CarloMara/didactic-octo-PSU/basette/basetta_lineare/lineare_rev3/docs/SR_Passives-1801.pdf

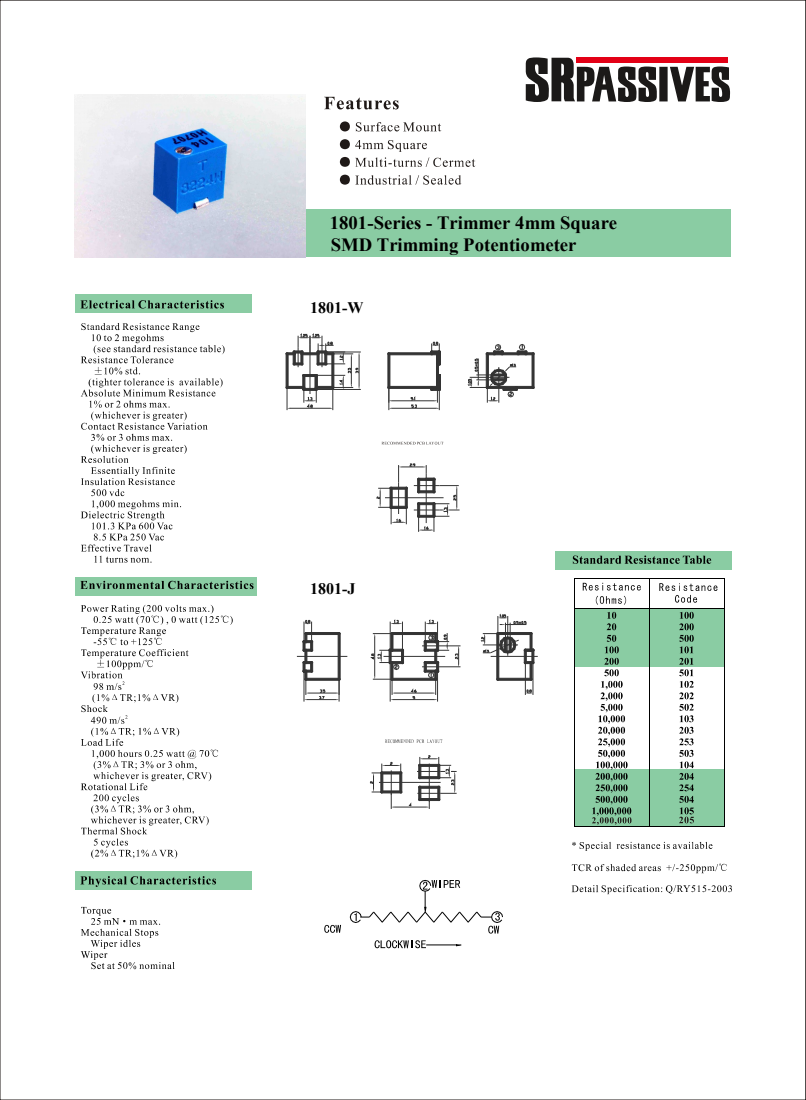
[picture p15: page 1]

1801-Series - Trimmer 4mm Square
SMD Trimming Potentiometer
