CarloMara/didactic-octo-PSU/basette/basetta_lineare/lineare_cv/output.pdf/alimentatore.pdf

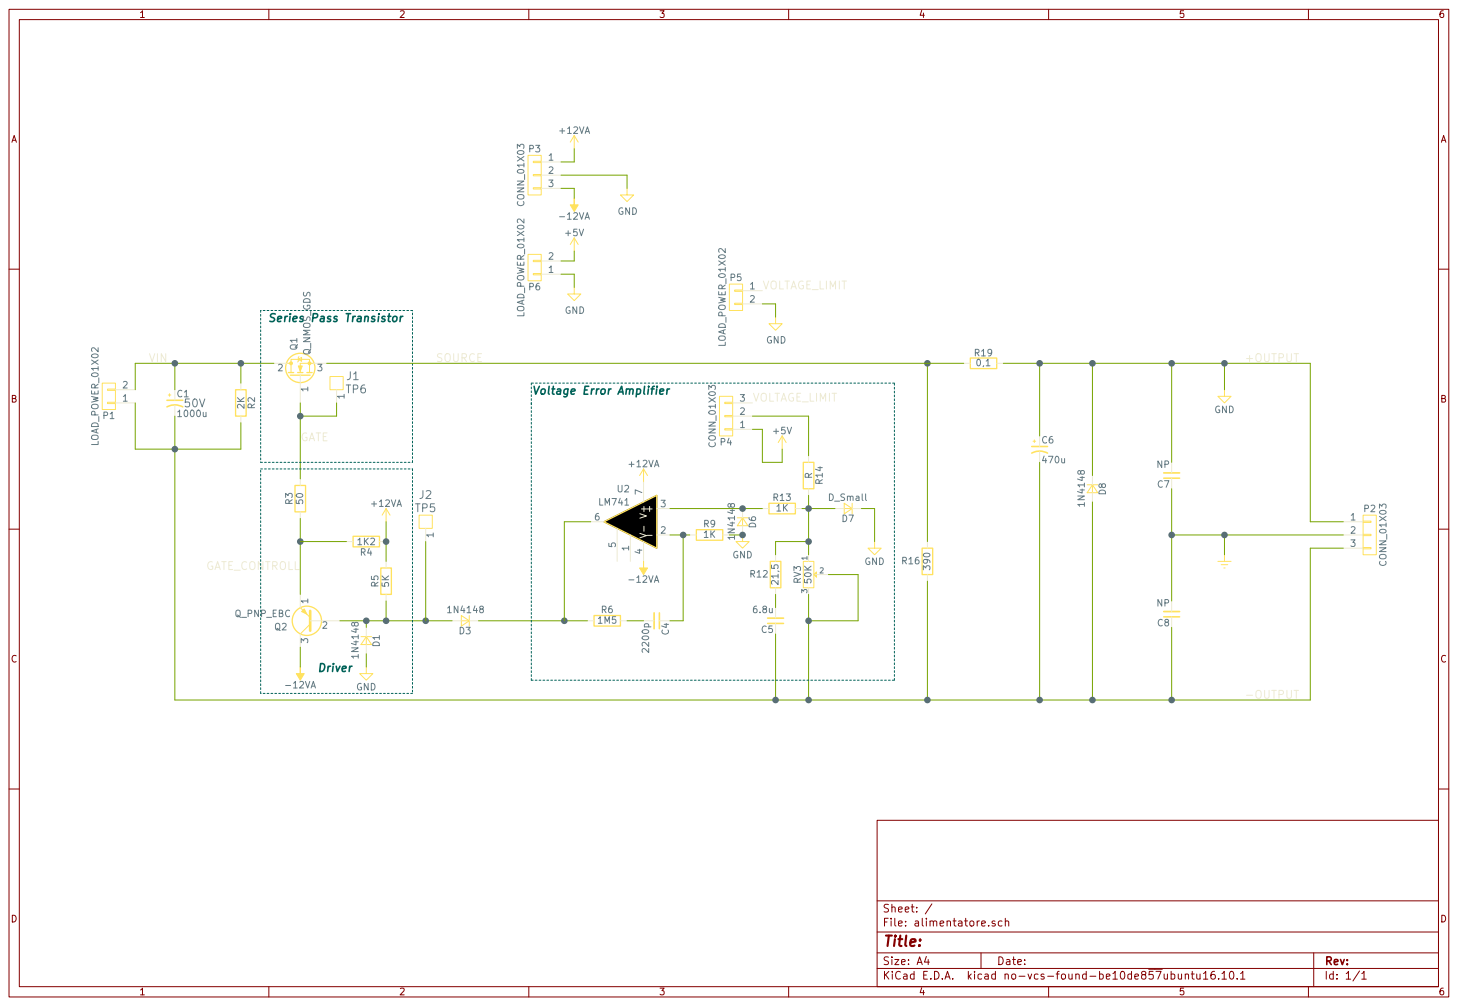
[picture p18: page 1]

Id: 1/1 Title: File: alimentatore.sch Sheet: /
