CarloMara/didactic-octo-PSU/basette/basetta_lineare/lineare_cv/output/alimentatore.pdf

Id: 1/1 Title: File: alimentatore.sch Sheet: /
