CarloMara/didactic-octo-PSU/simulazioni_spice/boost_buck.asc

C1: cap; 10µ; Rser=.01
C3: cap; 68n
C4: cap; 68n
C5: cap; 4.7µ
C6: cap; 4700p
C7: cap; 10p
C8: cap; 22µ; x2; Rser=.005
C9: cap; 470p
C11: cap; 10n
D1: schottky; PMEG2010AEB
L1: ind; 6.8µ; Ipk=5.94 Rser=0.014018 Rpar=640.56 Cpar=0 mfg="Coilcraft" pn="MSS1048-682"
Q1: pnp; 2N3906
R4: res; 27.4K
R5: res; 21K
R6: res; 10K
R7: res; 3k
U1: LTC3114-1
V1: voltage; 12
V2: voltage; 21
Named nets: 0, IN, OUT
.tran 3m startup
LTC3114-1 - 40V, 1A Synchronous Buck-Boost DC/DC Converter with Programmable Output Current 
Wide Vin Range Regulator with Bootstrapped LDO
Input: 2.7V to 40V     Output: 5V @ 1A for Vin > Vout
Notes: 
  If the simulation model is not found please update with the "Sync Release" command from the "Tools" menu.
  It remains the customer's responsibility to verify proper and reliable operation in the actual application.
  Component substitution and printed circuit board layout may significantly affect circuit performance or reliability.
  Contact your local sales representative for assistance. This circuit is distributed to customers only for use with LTC parts.
  Copyright © 2015 Linear Technology Inc.  All rights reserved.
D1 Improves 
Efficiency at High Vin
