CarloMara/didactic-octo-PSU/simulazioni_spice/switching_tracking/Switching_Follower_pass.asc

C1: POLCAP; 230µ; Rser=0.05
C2: POLCAP; 250µ; Rser=0.07
C3: cap; .01µ
C4: cap; 470p
C6: cap; 2200pf
D1: schottky; MBRS140
D2: diode; 1N4148
L1: IND; 50µ
M1: nmos; IRF510
Q1: pnp; 2N3906
Q2: pnp; 2N3906
R1: RES; 2.7K
R2: res; 10K
R3: res; 3k
R4: res; 1.5m
R5: res; 8k
R6: res; 5
R7: res; 10k
R8: res; 150k
R9: res; 5k
R10: res; 1.2k
U1: LT1074
U2: OP27
V1: VOLTAGE; 30; Rser=0.02
V2: voltage; 12
V3: voltage; 12
V4: voltage; 5
Named nets: 0, PREREG_OUT, IN, OUT, v+, v-, 5v, vgnd
.tran 10m uic
