CarloMara/didactic-octo-PSU/simulazioni_spice/switching_tracking/LT1074_TA01.asc

C1: POLCAP; 230µ; Rser=0.05
C2: POLCAP; 500µ; Rser=0.07
C3: cap; .01µ
D1: schottky; MBRS140
L1: IND; 50µ
R1: RES; 2.7K
R2: RES; 2.21K
R3: RES; 2.8K
Rload: res; 1
U1: LT1074
V1: VOLTAGE; 25; Rser=0.02
Named nets: 0, OUT, IN
.tran 2m startup
LT1074 - Step-Down Switching Regulator
Input: 10V to 40V       Output: 5V @ 5A
Note:
  If the simulation model is not found please update with the "Sync Release" command from the "Tools" menu.
  It remains the customer's responsibility to verify proper and reliable operation in the actual application.
  Component substitution and printed circuit board layout may significantly affect circuit performance or reliability.
  Contact your local sales representative for assistance. This circuit is distributed to customers only for use with LTC parts.
  Copyright © 2011 Linear Technology Inc. All rights reserved.
