CarloMara/didactic-octo-PSU/simulazioni_spice/switching_tracking/Switching_Follower.asc

C1: POLCAP; 230µ; Rser=0.05
C2: POLCAP; 500µ; Rser=0.07
C3: cap; .01µ
C4: cap; 470p
C5: cap; 100µ
D1: schottky; MBRS140
I1: current; SINE(1 1 1k)
L1: IND; 50µ
Q1: pnp; 2N3906
R1: RES; 2.7K
R2: res; 10K
R3: res; 5K
U1: LT1074
U2: LT3083
V1: VOLTAGE; 25; Rser=0.02
V2: VOLTAGE; 10; Rser=0.02
Named nets: 0, PREREG_OUT, IN, OUT
.tran 0 10m 4m
LT1074 - Step-Down Switching Regulator
Input: 10V to 40V       Output: 5V @ 5A
Note:
  If the simulation model is not found please update with the "Sync Release" command from the "Tools" menu.
  It remains the customer's responsibility to verify proper and reliable operation in the actual application.
  Component substitution and printed circuit board layout may significantly affect circuit performance or reliability.
  Contact your local sales representative for assistance. This circuit is distributed to customers only for use with LTC parts.
  Copyright © 2011 Linear Technology Inc. All rights reserved.
