CarloMara/didactic-octo-PSU/simulazioni_spice/varie/Draft1.asc

C1: cap; 2200pf
D1: diode; 1N4148
M1: nmos; BSZ42DN25NS3
Q1: pnp; 2N3906
R1: res; 1.5m
R2: res; 8k
R3: res; 10k
R4: res; 50k
R5: res; 5k
R6: res; 1.2k
R7: res; 100k
U1: OP27
V1: voltage; 12
V2: voltage; 12
V3: voltage; 5
V4: voltage; 40
Named nets: v-, v+, 0, 5v, vgnd
.tran 5m
