CarloMara/didactic-octo-PSU/simulazioni_spice/varie/LT3081_LT8612_LTC3632_LT3092_DC2132A.asc

C1: cap; .01µ
C2: cap; 1µ
C3: cap; .1µ
C4: cap; 10µ; x5; Rser=0.005
C6: cap; 10µ
C7: cap; 100µ; Rser=0.005
C8: cap; 10µ; x3; Rser=0.005
C9: cap; 1µ; Rser=0.005
C10: cap; 10µ; x3; Rser=0.005
C11: cap; .01µ
D1: diode; 1N4148
L1: ind; 5.5µ; Ipk=9.5 Rser=0.0103 Rpar=2100 Cpar=3.89p mfg="Wurth Elektronik" pn="744325550 WE-HCI 1050"
Q1: pnp; 2N3906
R1: res; 60.4K
R2: res; 54.6K
R3: res; 499K
R4: res; 10K
R5: res; 1K
R6: res; 104K
R7: res; 10K
R8: res; 1K
R9: res; 10K
R10: res; 10m
R11: res; 10m
R13: res; {x}
R14: res; 4.99K
R15: res; 100K
R22: res; 10K
R23: res; 10K
Rload: res; 10k
U1: LT8612
U2: LT3081
U3: LT3081
V1: voltage; 25
Named nets: 0, IN, OUT
.tran 0 6m 2m uic
LT3081 - 1.5A Single Resistor Rugged Linear Regulator with Monitors
LT8612 - 42V, 6A Synchronous Step-Down Regulator with 3µA Quiescent Current
LTC3632 - High Efficiency, High Voltage 20mA Synchronous Step-Down Converter
LT3092 - 200mA 2-Terminal Programmable Current Source
24V 3A Constant Voltage, Constant Current Bench Supply
Input: 10V to 40V     Output: 0V to 25V @ 0 to 3.1A
Note:
  Details description of this circuit is available in July 2014 edition of LT Journal of Analog Inovation.
  A smaller RUN/SS capacitors on the LT8612 is being used to reduce simulation time. The typical value should be 0.1µF.
  If the simulation model is not found please update with the "Sync Release" command from the "Tools" menu.
  It remains the customer's responsibility to verify proper and reliable operation in the actual application.
  Component substitution and printed circuit board layout may significantly affect circuit performance or reliability.
  Contact your local sales representative for assistance. This circuit is distributed to customers only for use with LTC parts.
  Copyright © 2015 Linear Technology Inc. All rights reserved.
Vout
Adjust
Ilim
Adjust
.step param x list 1k 5k 10k
