CarloMara/didactic-octo-PSU/simulazioni_spice/varie/LT8612_DC2010A_TA01A.asc

C1: cap; 1µ
C2: cap; 1n
C3: cap; .1µ
C4: cap; 100µ; V=10 Irms=0 Rser=0.003 Lser=0
C5: cap; 10p
C6: cap; 10µ
L1: ind; 3.3µ; Ipk=3.9 Rser=0.033 Rpar=5905 Cpar=3.85p
R1: res; 60.4K
R2: res; 1Meg
R3: res; 107k
R5: res; 100
U2: LT8612
V1: voltage; 12
V2: voltage; 1.7
Named nets: 0, OUT, IN
.tran 2m startup
LT8612 - 42V, 6A Synchronous Step-Down Regulator with 3µA Quiescent Current
µPower Buck Converter
Input: 5.8V to 42V     Output: 5V @ 6A, Fsw=700KHz
Note:
  A smaller SS capacitor is being used to reduce simulation time. See datasheet for typical values.
  If the simulation model is not found please update with the "Sync Release" command from the "Tools" menu.
  It remains the customer's responsibility to verify proper and reliable operation in the actual application.
  Component substitution and printed circuit board layout may significantly affect circuit performance or reliability.
  Contact your local sales representative for assistance. This circuit is distributed to customers only for use with LTC parts.
  Copyright© 2014 Linear Technology Inc. All rights reserved.
