CarloMara/didactic-octo-PSU/simulazioni_spice/varie/MODDED.asc

C1: cap; 0.001µ
C2: cap; 1µ
C3: cap; .1µ
C4: cap; 10µ; x5; Rser=0.005
C6: cap; 10µ
C7: cap; 100µ; Rser=0.005
C8: cap; 2200pf
C13: cap; 1µ
D1: diode; 1N4148
L1: ind; 5.5µ; Ipk=9.5 Rser=0.0103 Rpar=2100 Cpar=3.89p mfg="Wurth Elektronik" pn="744325550 WE-HCI 1050"
M1: nmos; BSP89
Q1: pnp; 2N3906
Q2: pnp; 2N3906
R1: res; 60.4K
R2: res; 54.6K
R3: res; 499K
R4: res; 1.5m
R5: res; 8k
R6: res; 5k
R7: res; 10k
R8: res; 5k
R9: res; 1.2k
R10: res; 50k
R11: res; 10K
R13: res; 1k
R14: res; 10k
R15: res; 22k
R16: res; 10K
U1: LT8612
U2: OP27
V1: voltage; 50
V2: voltage; 12
V3: voltage; 12
V4: voltage; 5
Named nets: 0, IN, v+, v-, 5v, vgnd, FB, VSW, VPART
LT3081 - 1.5A Single Resistor Rugged Linear Regulator with Monitors
LT8612 - 42V, 6A Synchronous Step-Down Regulator with 3µA Quiescent Current
LTC3632 - High Efficiency, High Voltage 20mA Synchronous Step-Down Converter
LT3092 - 200mA 2-Terminal Programmable Current Source
24V 3A Constant Voltage, Constant Current Bench Supply
Input: 10V to 40V     Output: 0V to 25V @ 0 to 3.1A
Note:
  Details description of this circuit is available in July 2014 edition of LT Journal of Analog Inovation.
  A smaller RUN/SS capacitors on the LT8612 is being used to reduce simulation time. The typical value should be 0.1µF.
  If the simulation model is not found please update with the "Sync Release" command from the "Tools" menu.
  It remains the customer's responsibility to verify proper and reliable operation in the actual application.
  Component substitution and printed circuit board layout may significantly affect circuit performance or reliability.
  Contact your local sales representative for assistance. This circuit is distributed to customers only for use with LTC parts.
  Copyright © 2015 Linear Technology Inc. All rights reserved.
.tran 4m uic
