CarloMara/didactic-octo-PSU/simulazioni_spice/varie/rail2rail.asc

C1: cap; 100µ
C6: cap; 10µ
C8: cap; 1200pf
D1: diode; 1N4148
I1: load2; PULSE(1 2 0 0.1m 0.1m 0.1m 1)
M1: nmos; IRF530
Q2: pnp; 2N3906
R4: res; 1.5m
R5: res; 8k
R6: res; 5k
R7: res; 10k
R8: res; 35k
R9: res; 1.2k
U2: OP27
V1: voltage; 30
V2: voltage; 15
V3: voltage; 15
V4: voltage; 5
Named nets: 0, IN, v+, v-, 5v, vgnd, VSW
.tran 0 10m 0 0.001m
