CarloMara/didactic-octo-PSU/simulazioni_spice/transistor_mosfet/transistor_mosfet.asc

M1: nmos; BSZ42DN25NS3
Q1: npn; 2N3055
R1: res; 40
R2: res; 1k
R3: res; 1k
R4: res; 1k
U2: OP27
V1: voltage; 15
V2: voltage; 15
V3: voltage; 1
Named nets: 0, v-, v+, vout
.tran 0 1u 0 0.01u
Configurazione avanzata usando un bjt(npn) per comandare un mosfet di tipo n
Il circuito può essere visto come un amplificatore non invertente (G=rf/ri+1)
il valore di vout sarò quindi il doppio della tensone che applichiamo attraverso il generaore V3, cche sarà poi sostituito da un DAC
al variare della corrente assorbita dal carico la tensione non cambia, quindi il circuito stà regolando in maniera opportuna
