CarloMara/didactic-octo-PSU/simulazioni_spice/transistor_mosfet_corrente/Draft2.asc

R19: res; 5K
R20A: res; 50k
R20B: res; 1
R28: res; 6.81k
R31: res; 10k
R40: res; 267k
U2: OP37
V1: voltage; 15
V2: voltage; 15
V3: voltage; 50v
V4: voltage; 0
Named nets: 0, V+, V-, CREF
.tran 0 1u 0 0.1u
-2.9744198V
