CarloMara/didactic-octo-PSU/simulazioni_spice/transistor_mosfet_corrente_guadagno/transistor_mosfet_corrente_guadagno.asc

D1: diode; 1N4148
D2: diode; 1N4148
D3: diode; 1N4148
M1: nmos; BSZ42DN25NS3
Q1: pnp; 2N3906
R1: res; 4.7k
R2: res; 1k
R3: res; 1k
R4: res; 1k
R5: res; 10m
R6: res; 1k
R7: res; {x}
R8: res; 1k
R9: res; {x}
R10: res; 1k
R11: res; 1k
R12: res; 4.7k
RL: res; 2
U1: OP27
U2: OP27
U3: OP27
U4: OP27
V1: voltage; 15
V2: voltage; 15
V3: voltage; 1
V4: voltage; -1
V5: voltage; 500m
Named nets: 0, v-, v+, vout, Iout
.tran 0 100u 0 0.01u
Configurazione avanzata usando un bjt(npn) per comandare un mosfet di tipo n
Il circuito può essere visto come un amplificatore non invertente (G=rf/ri+1)
il valore di vout sarò quindi il doppio della tensone che applichiamo attraverso il generaore V3, cche sarà poi sostituito da un DAC
al variare della corrente assorbita dal carico la tensione non cambia, quindi il circuito stà regolando in maniera opportuna
.step param x 1k 100k 10k
