CarloMara/didactic-octo-PSU/simulazioni_spice/varie/transistor_mosfet_E361.asc

C1: cap; 100n
D1: diode; 1N4148
D2: diode; 1N4148
D3: diode; 1N4148
M1: nmos; BSZ42DN25NS3
Q1: pnp; 2N3906
R1: res; 4.7k
R2: res; 1k
R3: res; 1k
R4: res; 1k
R5: res; .1
R6: res; 1K
R7: res; 49K
R12: res; 4.7k
RL: res; 1
U1: OP27
U2: OP27
U3: OP27
V1: voltage; 15
V2: voltage; 15
V3: voltage; 0.5
V4: voltage; 15
V5: voltage; 2.5
Named nets: 0, v-, v+, vout, vcc, v0
.tran 0 100u 0 0.01u
Configurazione avanzata usando un bjt(npn) per comandare un mosfet di tipo n
Il circuito può essere visto come un amplificatore non invertente (G=rf/ri+1)
il valore di vout sarò quindi il doppio della tensone che applichiamo attraverso il generaore V3, cche sarà poi sostituito da un DAC
al variare della corrente assorbita dal carico la tensione non cambia, quindi il circuito stà regolando in maniera opportuna
