CarloMara/didactic-octo-PSU/basette/basette_test/basetta_test_switching/sw_48@2_sch/2017-02-08_13-06-18/2017-02-08_13-06-18.sch

## EAGLE design basette/basette_test/basetta_test_switching/sw_48@2_sch/2017-02-08_13-06-18/2017-02-08_13-06-18.sch (2017-02-09)

Schematic: 2017-02-08_13-06-18.sch

Parts:
D2: 550mV; SOD-123F
D3: 700mV; SMB
GND, GND1, GND2, GND3, GND4, GND6, GND7, GND8: WB_GND
L1: 8.2uH; XAL1010
M1, M2: 25V; DQG0008A
M3: 100V; TRANS_NexFET_Q5A
M4: 60V; TRANS_NexFET_Q5A
U1: LM5175PWPR; PWP0028F_N
_CSG_1, _CSG_2: WB_CONTINUATION
_HDRV1_1, _HDRV1_2, _HDRV2_1, _HDRV2_2: WB_CONTINUATION
_ISNS+_1, _ISNS+_2: WB_CONTINUATION
_ISNS-_1, _ISNS-_2: WB_CONTINUATION
_LDRV1_1, _LDRV1_2, _LDRV2_1, _LDRV2_2: WB_CONTINUATION
_RCS_1, _RCS_2: WB_CONTINUATION
_SW1_1, _SW1_2, _SW2_1, _SW2_2: WB_CONTINUATION
